mcculloughembedded/3435/collateral/renders/back.png

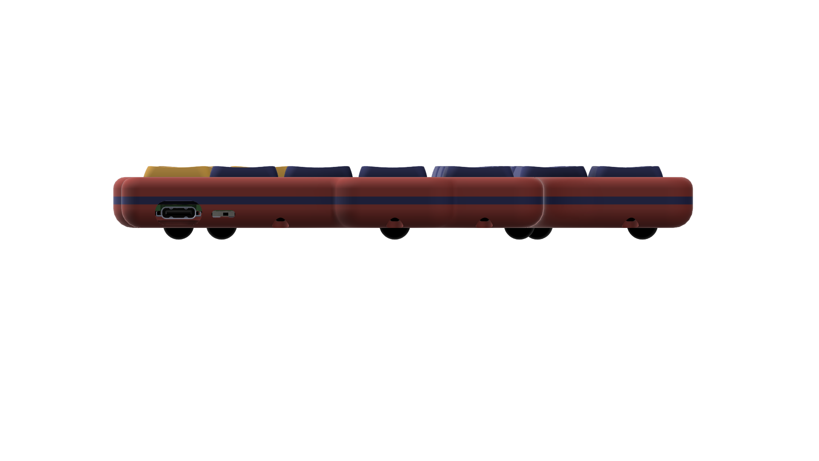
collateral/renders/back.png
