mcculloughembedded/3435/collateral/renders/both-sides-iso.png

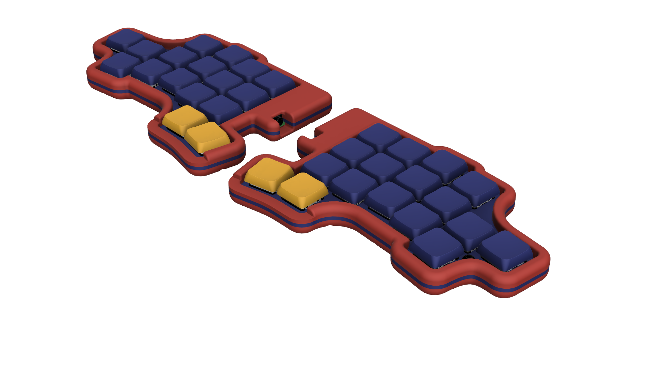
collateral/renders/both-sides-iso.png
