mcculloughembedded/3435/collateral/renders/both-sides-user-view.png

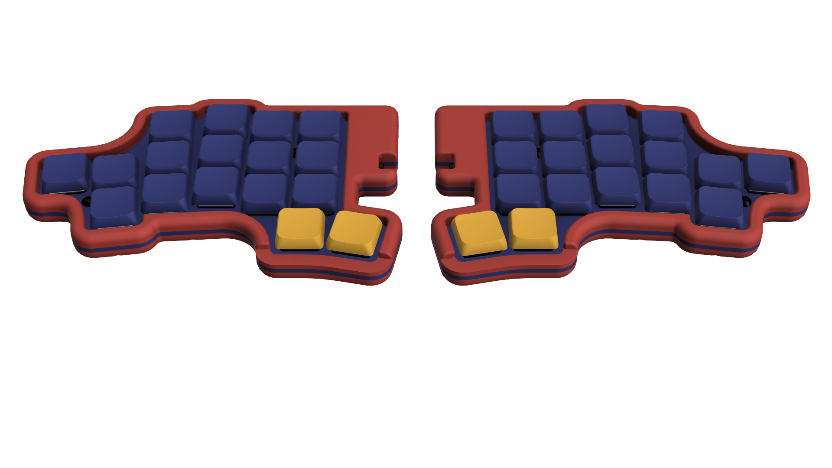
collateral/renders/both-sides-user-view.png
