mcculloughembedded/3435/collateral/renders/bottom.png

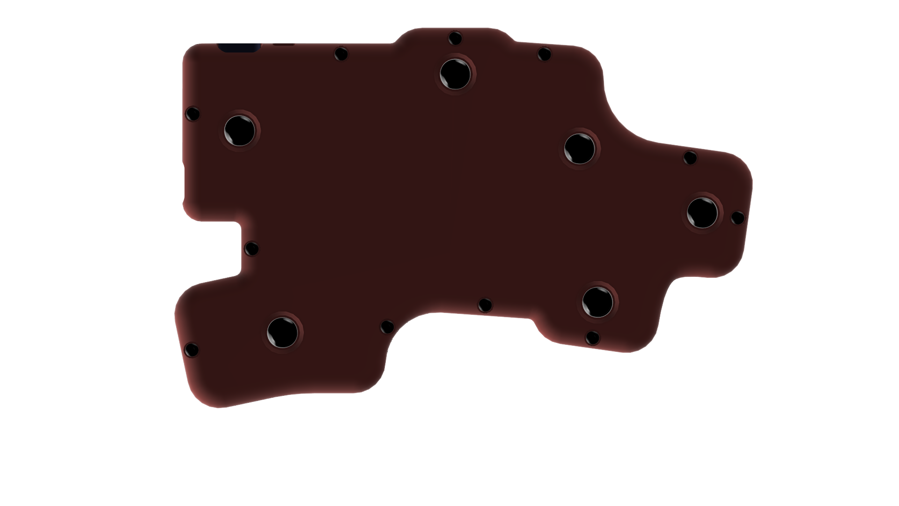
collateral/renders/bottom.png
