mcculloughembedded/3435/collateral/renders/exploded-iso.png

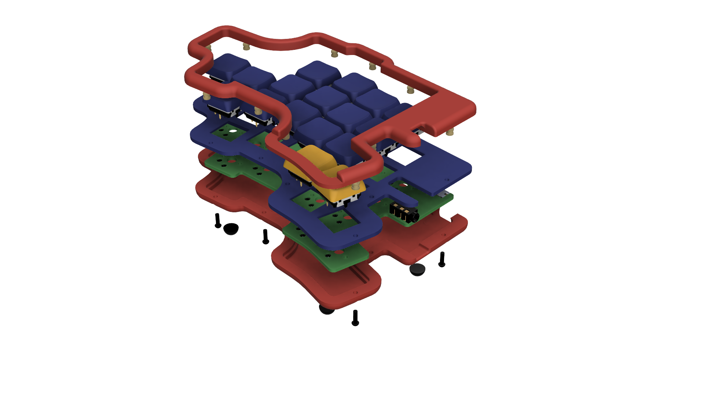
collateral/renders/exploded-iso.png
