mcculloughembedded/3435/collateral/renders/iso-2.png

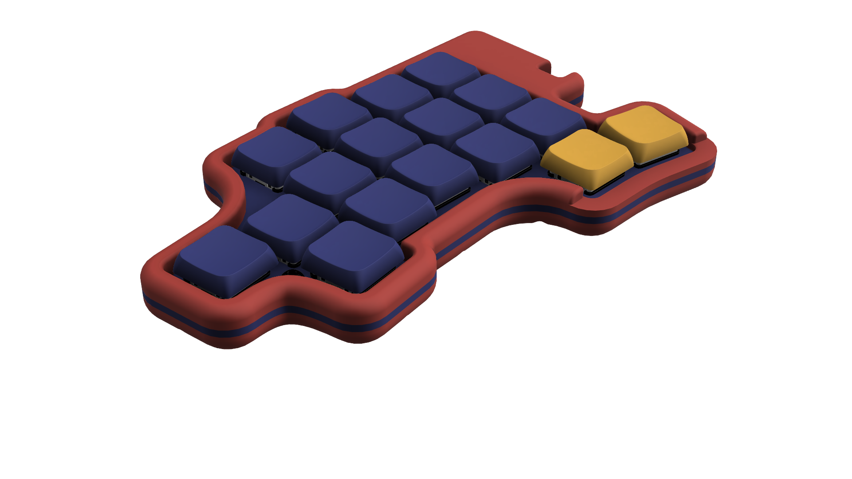
collateral/renders/iso-2.png
