mcculloughembedded/3435/collateral/renders/iso.png

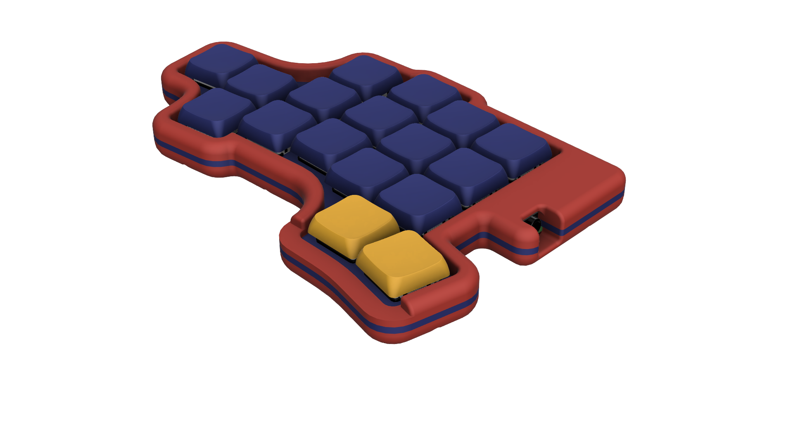
collateral/renders/iso.png
